DanielFromRice/JukeboxHero/SD_code/mmc.c

/*-----------------------------------------------------------------------*/
/* Low level disk I/O module skeleton for Petit FatFs (C)ChaN, 2009      */
/*-----------------------------------------------------------------------*/

/*-----------------------------------------------------------------------*/
/* mmc.c msp430 USCI support routines                                          */
/*-----------------------------------------------------------------------*/

#include <msp430.h>
#include <stdint.h>
#include <stdio.h>

#include "SPI.h"
#include "diskio.h"
#include "pff.h"
#include "mmc.h"

#define DELAY_100US() __delay_cycles(100)  /* ( 100us/(1/16Mhz) )  = 1600 ticks */
#define SELECT()    P1OUT &= ~BIT5      /* CS = L */
#define DESELECT()  P1OUT |= BIT5       /* CS = H */
#define MMC_SEL     !(P1OUT & BIT5)     /* CS status (true:CS == L) */

/* Definitions for MMC/SDC command */
#define CMD0    (0x40+0)    /* GO_IDLE_STATE */
#define CMD1    (0x40+1)    /* SEND_OP_COND (MMC) */
#define ACMD41  (0xC0+41)   /* SEND_OP_COND (SDC) */
#define CMD8    (0x40+8)    /* SEND_IF_COND */
#define CMD16   (0x40+16)   /* SET_BLOCKLEN */
#define CMD17   (0x40+17)   /* READ_SINGLE_BLOCK */
#define CMD24   (0x40+24)   /* WRITE_BLOCK */
#define CMD55   (0x40+55)   /* APP_CMD */
#define CMD58   (0x40+58)   /* READ_OCR */

/* Card type flags (CardType) */
#define CT_MMC              0x01    /* MMC ver 3 */
#define CT_SD1              0x02    /* SD ver 1 */
#define CT_SD2              0x04    /* SD ver 2 */
#define CT_BLOCK            0x08    /* Block addressing */

static BYTE CardType;

/*-----------------------------------------------------------------------*/
/* Send a command packet to MMC                                          */
/*-----------------------------------------------------------------------*/

static BYTE send_cmd(BYTE cmd, /* 1st byte (Start + Index) */
DWORD arg /* Argument (32 bits) */
) {
    BYTE n, res;

    if (cmd & 0x80) { /* ACMD<n> is the command sequense of CMD55-CMD<n> */
        cmd &= 0x7F;
        res = send_cmd(CMD55, 0);
        if (res > 1)
            return res;
    }

    /* Select the card */DESELECT();
    spi_receive();
    SELECT();
    spi_receive();

    /* Send a command packet */
    spi_send((BYTE) cmd); /* Start + Command index */
    spi_send((BYTE) (arg >> 24)); /* Argument[31..24] */
    spi_send((BYTE) (arg >> 16)); /* Argument[23..16] */
    spi_send((BYTE) (arg >> 8)); /* Argument[15..8] */
    spi_send((BYTE) arg); /* Argument[7..0] */
    n = 0x01; /* Dummy CRC + Stop */
    if (cmd == CMD0)
        n = 0x95; /* Valid CRC for CMD0(0) */
    if (cmd == CMD8)
        n = 0x87; /* Valid CRC for CMD8(0x1AA) */
    spi_send(n);

    /* Receive a command response */
    n = 10; /* Wait for a valid response in timeout of 10 attempts */
    do {
        res = spi_receive();
    } while ((res & 0x80) && --n);

    return res; /* Return with the response value */
}

/*-----------------------------------------------------------------------*/
/* Initialize Disk Drive                                                 */
/*-----------------------------------------------------------------------*/

DRESULT disk_initialize(void) {
    BYTE n, cmd, ty, ocr[4];
    UINT tmr;

#if _USE_WRITE
    if (CardType && MMC_SEL)
        disk_writep(0, 0); /* Finalize write process if it is in progress */
#endif
    spi_set_divisor(SPI_250kHz);

    DESELECT();
    for (n = 10; n; n--)
        spi_receive(); /* 80 dummy clocks with CS=H */

    ty = 0;
    if (send_cmd(CMD0, 0) == 1) { /* Enter Idle state */
        if (send_cmd(CMD8, 0x1AA) == 1) { /* SDv2 */
            for (n = 0; n < 4; n++)
                ocr[n] = spi_receive(); /* Get trailing return value of R7 resp */
            if (ocr[2] == 0x01 && ocr[3] == 0xAA) { /* The card can work at vdd range of 2.7-3.6V */
                for (tmr = 10000; tmr && send_cmd(ACMD41, 1UL << 30); tmr--)
                    DELAY_100US(); /* Wait for leaving idle state (ACMD41 with HCS bit) */
                if (tmr && send_cmd(CMD58, 0) == 0) { /* Check CCS bit in the OCR */
                    for (n = 0; n < 4; n++)
                        ocr[n] = spi_receive();
                    ty = (ocr[0] & 0x40) ? CT_SD2 | CT_BLOCK : CT_SD2; /* SDv2 (HC or SC) */
                }
            }
        } else { /* SDv1 or MMCv3 */
            if (send_cmd(ACMD41, 0) <= 1) {
                ty = CT_SD1;
                cmd = ACMD41; /* SDv1 */
            } else {
                ty = CT_MMC;
                cmd = CMD1; /* MMCv3 */
            }
            for (tmr = 10000; tmr && send_cmd(cmd, 0); tmr--)
                DELAY_100US(); /* Wait for leaving idle state */
            if (!tmr || send_cmd(CMD16, 512) != 0) /* Set R/W block length to 512 */
                ty = 0;
        }
    }
    CardType = ty;
    spi_set_divisor(SPI_DEFAULT_SPEED);
    DESELECT();
    spi_receive();

    return ty ? 0 : STA_NOINIT;
}

/*-----------------------------------------------------------------------*/
/* Read partial sector                                                   */
/*-----------------------------------------------------------------------*/

DRESULT disk_readp(BYTE *buff, /* Pointer to the read buffer (NULL:Read bytes are forwarded to the stream) */
DWORD lba, /* Sector number (LBA) */
WORD ofs, /* Byte offset to read from (0..511) */
WORD cnt /* Number of bytes to read (ofs + cnt mus be <= 512) */
) {
    DRESULT res;
    BYTE rc;
    WORD bc;

    if (!(CardType & CT_BLOCK))
        lba *= 512; /* Convert to byte address if needed */

    res = RES_ERROR;
    if (send_cmd(CMD17, lba) == 0) { /* READ_SINGLE_BLOCK */

        bc = 40000;
        do { /* Wait for data packet */
            rc = spi_receive();
        } while (rc == 0xFF && --bc);

        if (rc == 0xFE) { /* A data packet arrived */
            bc = 514 - ofs - cnt;

            /* Skip leading bytes */
            if (ofs) {
                do
                    spi_receive();
                while (--ofs);
            }

            /* Receive a part of the sector */
            if (buff) { /* Store data to the memory */
                do {
                    *buff++ = spi_receive();
                } while (--cnt);
            } else { /* Forward data to the outgoing stream (depends on the project) */
                do {
//                    FORWARD(spi_receive());
                } while (--cnt);
            }

            /* Skip trailing bytes and CRC */
            do
                spi_receive();
            while (--bc);

            res = RES_OK;
        }
    }

    DESELECT();
    spi_receive();

    return res;
}

/*-----------------------------------------------------------------------*/
/* Write partial sector                                                  */
/*-----------------------------------------------------------------------*/

#if _USE_WRITE
DRESULT disk_writep(const BYTE *buff, /* Pointer to the bytes to be written (NULL:Initiate/Finalize sector write) */
DWORD sa /* Number of bytes to send, Sector number (LBA) or zero */
) {
    DRESULT res;
    WORD bc;
    static WORD wc;

    res = RES_ERROR;

    if (buff) { /* Send data bytes */
        bc = (WORD) sa;
        while (bc && wc) { /* Send data bytes to the card */
            spi_send(*buff++);
            wc--;
            bc--;
        }
        res = RES_OK;
    } else {
        if (sa) { /* Initiate sector write process */
            if (!(CardType & CT_BLOCK))
                sa *= 512; /* Convert to byte address if needed */
            if (send_cmd(CMD24, sa) == 0) { /* WRITE_SINGLE_BLOCK */
                spi_send(0xFF);
                spi_send(0xFE); /* Data block header */
                wc = 512; /* Set byte counter */
                res = RES_OK;
            }
        } else { /* Finalize sector write process */
            bc = wc + 2;
            while (bc--)
                spi_send(0); /* Fill left bytes and CRC with zeros */
            if ((spi_receive() & 0x1F) == 0x05) { /* Receive data resp and wait for end of write process in timeout of 500ms */
                for (bc = 5000; spi_receive() != 0xFF && bc; bc--)
                    DELAY_100US(); /* Wait ready */
                if (bc)
                    res = RES_OK;
            }
            DESELECT();
            spi_receive();
        }
    }

    return res;
}
#endif
