DanielFromRice/JukeboxHero/SD_code/SPI.h

//-----------------------------------------------------------------------------
// SPI.h - common function declarations for different SPI implementations
//-----------------------------------------------------------------------------
#ifndef SPI_H_
#define SPI_H_

/**
 * SMCLK divider arguments for spi_set_divisor
 * assumes 16MHz SMCLK. You need to change if you
 * use a different frequency
 */
//#define SPI_250kHz 64 /* 16MHz/250000 */
//#define SPI_400kHz 40 /* 16MHz/400000 */
//#define SPI_1MHz   16 /* 16MHz/1MHz */
//#define SPI_2MHz    8 /* 16MHz/2MHz */
//#define SPI_4MHz    4 /* 16MHz/4MHz */
//#define SPI_8MHz    2 /* 16MHz/8MHz */
//#define SPI_16MHz   1 /* 16MHz/16Mhz */

#define SPI_333kHz    3 /* 1MHz/333333 */
#define SPI_250kHz    4 /* 1MHz/250000 */
#define SPI_1MHz      1 /* 1MHz/1MHz */

#define SPI_DEFAULT_SPEED SPI_1MHz

#ifdef __cplusplus
extern "C" {
#endif

void spi_initialize(void);
uint8_t spi_send(const uint8_t);
uint8_t spi_receive(void);
uint16_t spi_set_divisor(const uint16_t clkdivider);

#ifdef __cplusplus
}++
#endif

#endif /*SPI_H_*/
